intergalaktik/ulx5m-m2/pic/ulx5m-m2-issue1.jpg

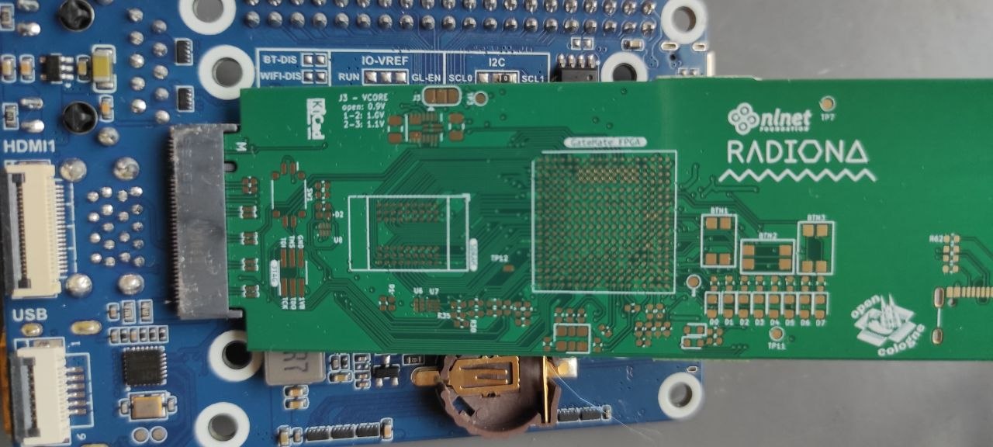
pic/ulx5m-m2-issue1.jpg
